bablokb/pcb-pic-devboard/pic-dev-board.test/quarz_4MHz.asm

;#################################################################
;## UP'e für Zeitverzögerungen mit Quarz 4,000 MHz /4 = 1 MHz :
;## Zykluszeit = 1/1000000 Hz = 1,0 µs                         
;#################################################################
;EQU's, z.B.:
;	miniteil	equ	0x20
;	miditeil	equ	0x21
;	maxiteil	equ	0x22
;	time0	equ	0x23
;	time1	equ	0x24
;	time2	equ	0x25
;#################################################################
;mini-, midi- oder maxitime: Verzögerung x-mal 100µs, 1ms oder 1/4s
;"x" (dezimal) muß als Parameter in W vorher geladen worden sein
;#################################################################
minitime
	movlb	d'0'
	movwf	miniteil	;"x"=W=miniteil
mm0	call	time100		;100µs Verzögerung
	movlb	d'0'
	decf	miniteil,F	;miniteil=miniteil-1
	btfss	STATUS,Z	;wenn Z=1, überspringe nä. Bef.
	goto	mm0		;Z=0, miniteil>0
	return			;Z=1, miniteil=0, Verzögerung erreicht
;
miditime
	movlb	d'0'
	movwf	miditeil	;"x"=W=miditeil
mm1	call	time1ms		;1ms Verzögerung
	movlb	d'0'
	decf	miditeil,F	;miditeil=miditeil-1
	btfss	STATUS,Z	;wenn Z=1, überspringe nä. Bef.
	goto	mm1		;Z=0, miditeil>0
	return			;Z=1, miditeil=0, Verzögerung erreicht
;
maxitime
	movlb	d'0'
	movwf	maxiteil	;"x"=W=maxiteil
mm2	call	time250ms	;250ms Verzögerung
	movlb	d'0'
	decf	maxiteil,F	;maxiteil=maxiteil-1
	btfss	STATUS,Z	;wenn Z=1, überspringe nä. Bef.
	goto	mm2		;Z=0, maxiteil>0
	return			;Z=1, maxiteil=0, Verzögerung erreicht
;
;#################################################################
;UP time100: Zeitschleife 100 µs (23x4=92+8=100 Zyklen a 1 µs)
;#################################################################
time100
	movlb	d'0'
	movlw	0x17		;W =17 hex , =23 dez
	movwf	time0		;w->time0
m0	decf	time0,F		;time0 decrem., wenn 0, Z=1
	btfss	STATUS,Z	;wenn Z=1, überspringe nä. Bef.
	goto	m0		;Z=0, weil time0 > 0, springe zu m0
	nop			;Z=1, weil time0 = 0
	nop			;
	return			;UP-Ende
;
;#################################################################
;UP time1ms: Zeitschleife 1 ms (248x4=992+8=1000 Zyklen a 1µs) 
;#################################################################
time1ms
	movlb	d'0'
	movlw	0xf8		;W =F8 hex , =248 dez
	movwf	time1		;w->time1
m1	decf	time1,F		;time1 decrem., wenn 0, Z=1
	btfss	STATUS,Z	;
	goto	m1		;
	nop
	nop
	return			;UP-Ende
;
;#################################################################
;UP time250ms: Zeitschleife 250 ms (250x1ms=250ms+6µs)
;#################################################################
time250ms
	movlw	0xfa		;W =FA hex , =250 dez
	movlb	d'0'
	movwf	time2		;w->time2
m2	call	time1ms		;Zeitverzögerung 1ms
	movlb	d'0'
	decf	time2,F		;time2 decrem., wenn 0, Z=1
	btfss	STATUS,Z	;wenn Z=1, überspringe nä. Bef.
	goto	m2
	return
;
;#################################################################
;Ende Datei quarz_4MHz.asm
